lipsumar/just-between-us/docs/JustBetweenUs.kicad_sch

## KiCad design docs/JustBetweenUs.kicad_sch (2025-04-03)

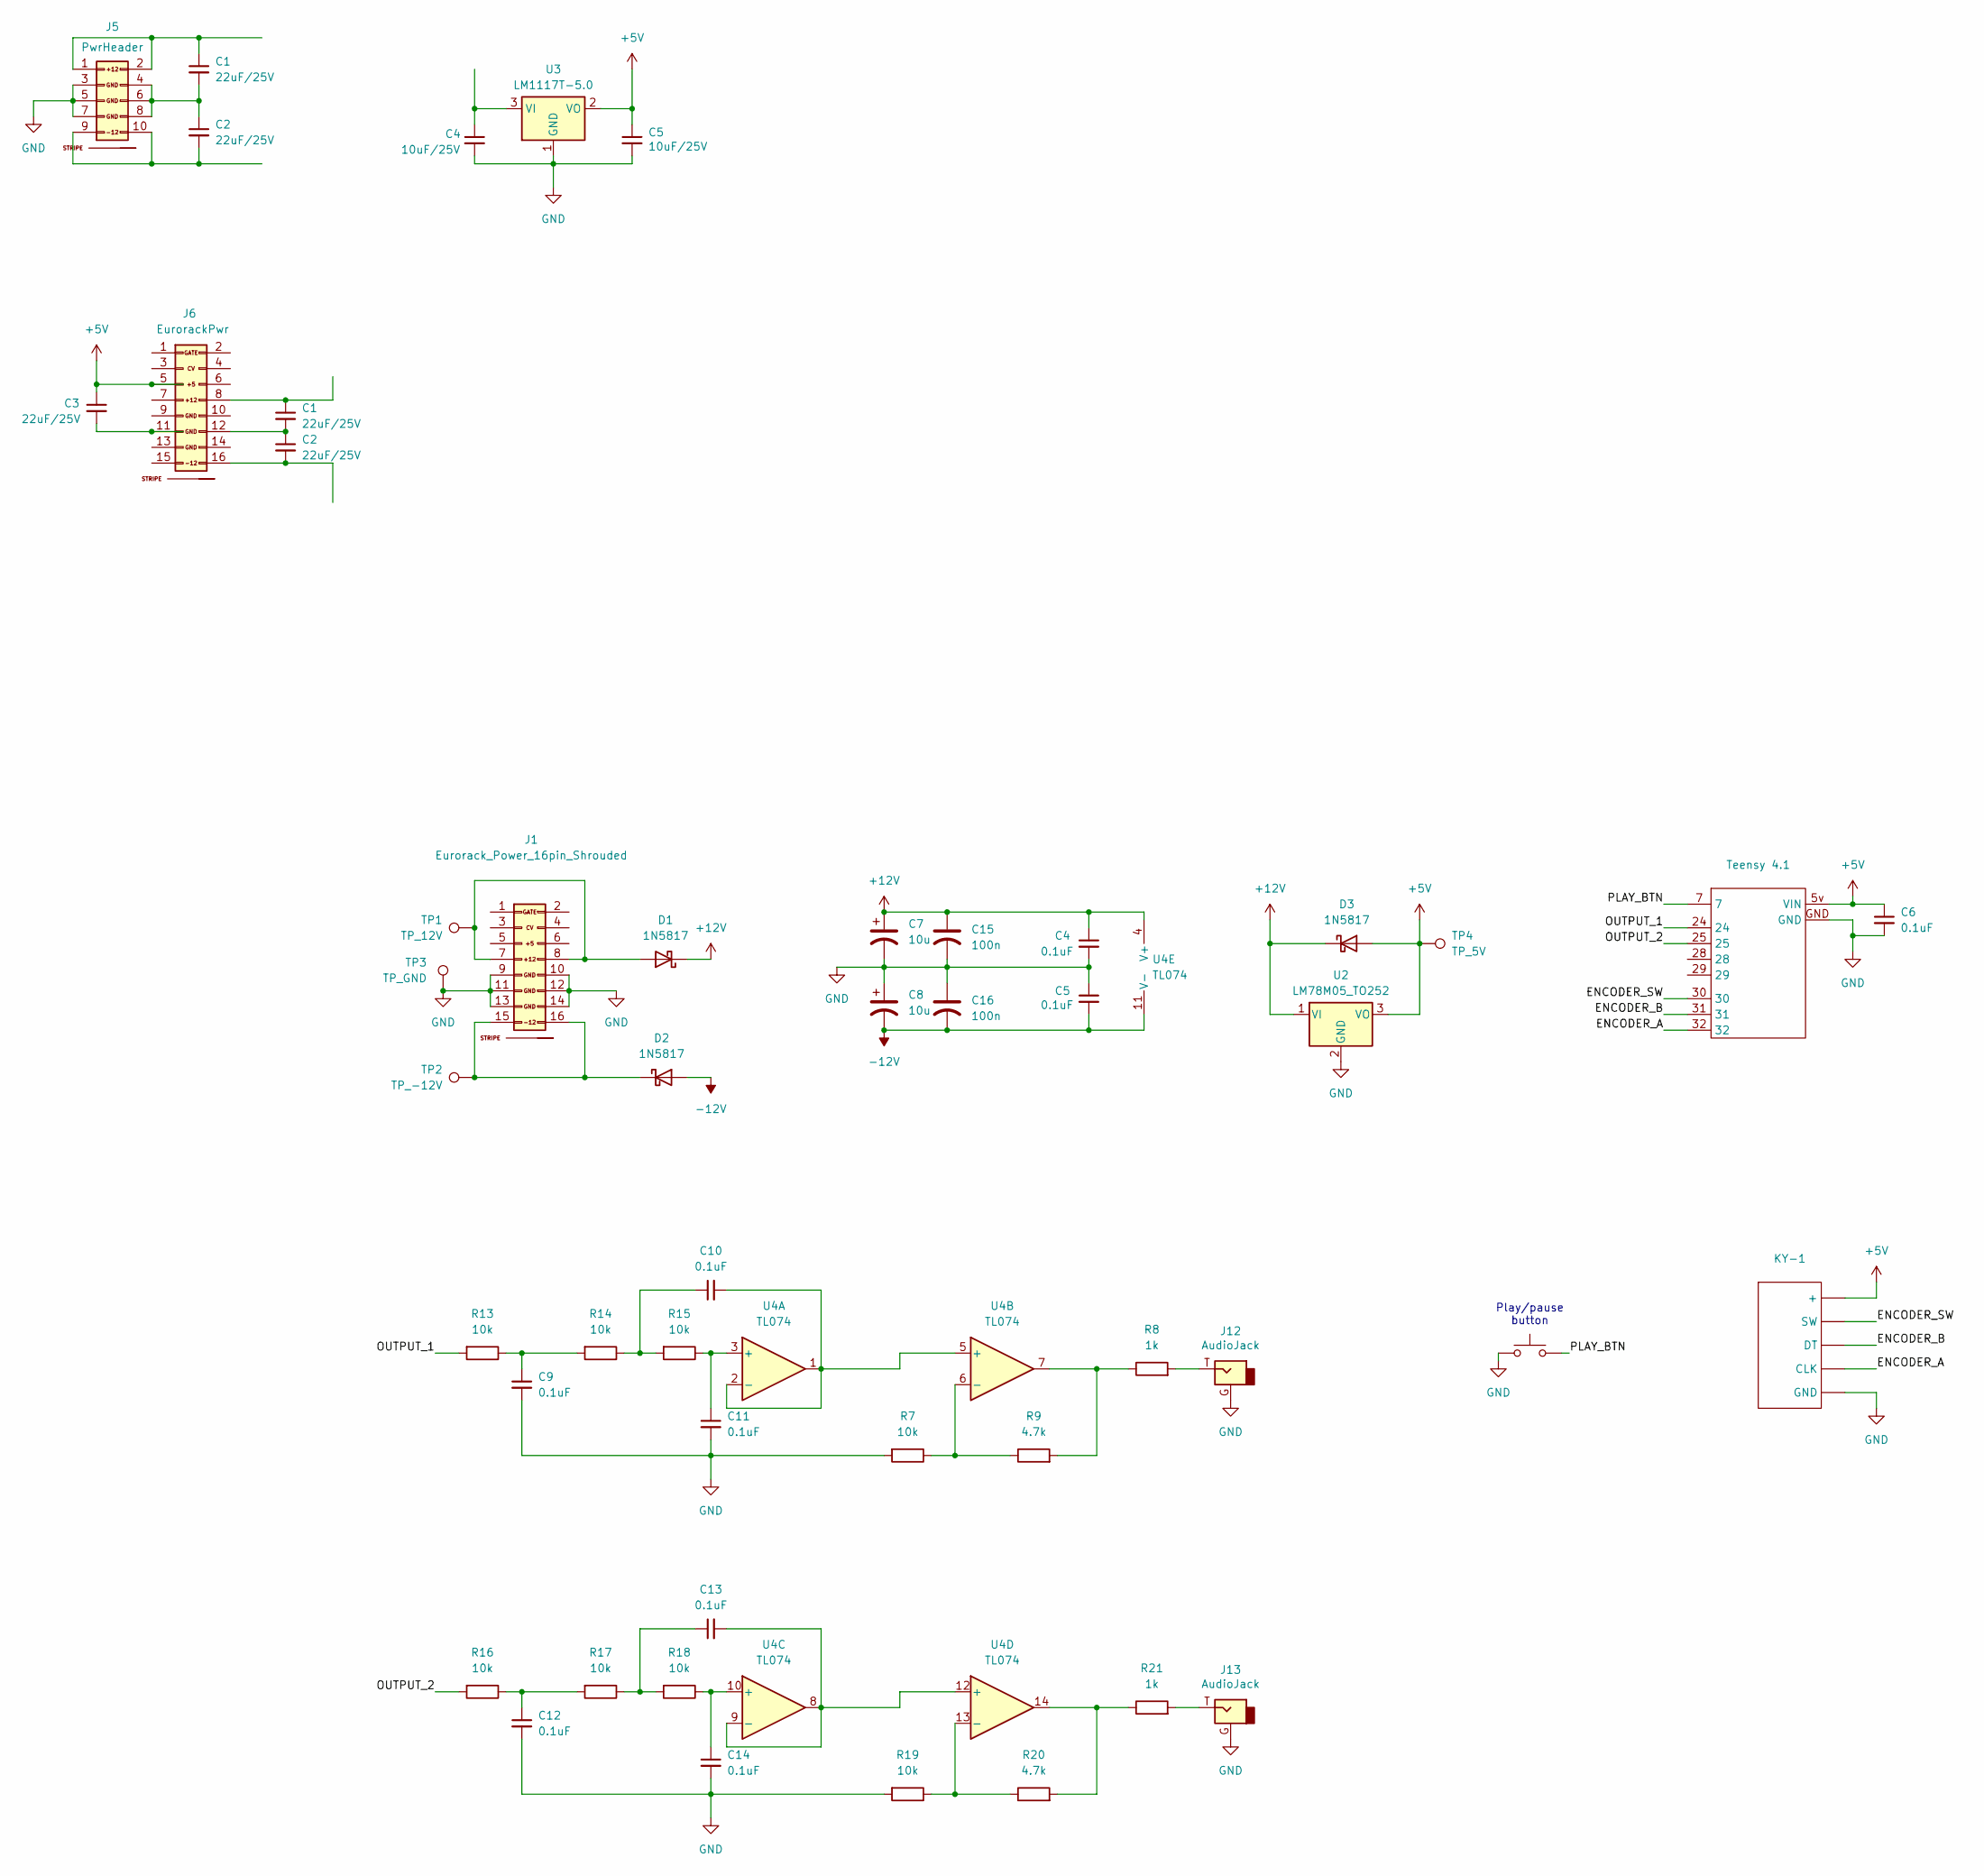
[picture p7: schematic JustBetweenUs.kicad_sch]

Parts:
C1, C2, C3: 22uF_0805_25V; C_0805; Part Number GRM21BR61E226ME44L; JLCPCB ID C45783
C4, C5: 10uF_0805_25V; C_0805; Part Number GRM21BR61E106MA73L; JLCPCB ID C15850
C6, C9, C10, C11, C12, C13, C14: 100nF_0603_16V; C_0603; Part Number 0603YC104KAT2A; JLCPCB ID C14663
C7, C8: 10u
C15, C16: 100n
D1, D2, D3: 1N5817; D_DO-41_SOD81_P10.16mm_Horizontal
J1: Eurorack_Power_16pin_Shrouded; Pins_2x08_2.54mm_TH_EuroPower_Shrouded; Part Number LL1007-1 (2*8 HITEMP)
J5: PwrHeader; Pins_2x05_2.54mm_TH_Europower; Part Number 1-1002FBV0T
J6: EurorackPwr; Pins_2x08_2.54mm_TH_EuroPower_Shrouded; Part Number LL1007-1 (2*8 HITEMP)
J12, J13: AudioJack
KY-1: (no value)
R7, R13, R14, R15, R16, R17, R18, R19: 10k_0603; R_0603; Part Number RC0603FR-0710KL; JLCPCB ID C25804
R8, R21: 1k_0603; R_0603; Part Number RC0603FR-071KL; JLCPCB ID C21190
R9, R20: 4.7k_0603; R_0603; Part Number RC0603FR-074K7L; JLCPCB ID C23162
SW3: SW_Push
TP1: TP_12V; TestPoint_Pad_D1.0mm
TP2: TP_-12V; TestPoint_Pad_D1.0mm
TP3: TP_GND; TestPoint_Pad_D1.0mm
TP4: TP_5V; TestPoint_Pad_D1.0mm
Teensy 4.1: (no value)
U2: LM78M05_TO252; TO-252-2
U3: LM1117T-5.0; TO-220-3_Vertical
U4: TL074

Connections:
+5V: C3.1, C5.1, C6.1, D3.2 (A), J6.5 (+12V), KY-1.2 (+), TP4.1, Teensy 4.1.5v (VIN), U2.3 (VO), U3.2 (VO)
+12V: C4.1, C7.1, C15.1, D1.1 (K), D3.1 (K), U2.1 (VI), U4.4 (V+)
-12V: C5.2, C8.2, C16.2, D2.2 (A), U4.11 (V-)
ENCODER_A: KY-1.5 (CLK), Teensy 4.1.32
ENCODER_B: KY-1.4 (DT), Teensy 4.1.31
ENCODER_SW: KY-1.3 (SW), Teensy 4.1.30
GND: C4.2, C5.1, C5.2, C6.2, C7.2, C8.1, C9.2, C11.2, C12.2, C14.2, C15.2, C16.1, J1.9 (GND), J1.10 (GND), J1.11 (GND), J1.12 (GND), J1.13 (-12), J1.14 (-12V), J5.3 (GND), J5.5 (GND), J5.7 (GND), J12.G, J13.G, KY-1.1 (GND), R7.2, R19.2, SW3.1, TP3.1, Teensy 4.1.GND, U2.2 (GND), U3.1 (GND)
unnamed: C1.1, J5.1 (+12V), J5.2 (+12V), J6.8 (+12V)
unnamed: C1.2, C2.1, J5.4 (GND), J5.6 (GND), J5.8 (GND), J6.12 (GND)
unnamed: C2.2, J5.9 (-12V), J5.10 (-12V), J6.16
unnamed: C3.2, J6.11 (GND)
unnamed: C4.1, U3.3 (VI)
unnamed: C9.1, R13.1, R14.2
unnamed: C10.1, R14.1, R15.2
unnamed: C10.2, U4.1, U4.2 (-), U4.5 (+)
unnamed: C11.1, R15.1, U4.3 (+)
unnamed: C12.1, R16.1, R17.2
unnamed: C13.1, R17.1, R18.2
unnamed: C13.2, U4.8, U4.9 (-), U4.12 (+)
unnamed: C14.1, R18.1, U4.10 (+)
unnamed: D1.2 (A), J1.7 (12V), J1.8 (+12V), TP1.1
unnamed: D2.1 (K), J1.15 (-12V), J1.16, TP2.1
unnamed: J12.T, R8.2
unnamed: J13.T, R21.2
unnamed: R7.1, R9.1, U4.6 (-)
unnamed: R8.1, R9.2, U4.7
unnamed: R19.1, R20.1, U4.13 (-)
unnamed: R20.2, R21.1, U4.14
OUTPUT_1: R13.2, Teensy 4.1.24
OUTPUT_2: R16.2, Teensy 4.1.25
PLAY_BTN: SW3.2, Teensy 4.1.7

Notes on the sheet:
Play/pause button
